TuriSc/Diapasonix/audio/audio_i2s.c

/*
 * Copyright (c) 2020 Raspberry Pi (Trading) Ltd.
 *
 * SPDX-License-Identifier: BSD-3-Clause
 *
 * Adapted from pico-extras/src/rp2_common/pico_audio_i2s/audio_i2s.c
 * Converted from C++ to C for this project.
 */

#include <stdio.h>
#include "audio_i2s.h"
#include "audio_i2s.pio.h"
#include "hardware/pio.h"
#include "hardware/gpio.h"
#include "hardware/dma.h"
#include "hardware/irq.h"
#include "hardware/clocks.h"
#include <assert.h>

#if PICO_AUDIO_I2S_MONO_OUTPUT
#define i2s_dma_configure_size DMA_SIZE_16
#else
#define i2s_dma_configure_size DMA_SIZE_32
#endif

#define audio_pio __CONCAT(pio, PICO_AUDIO_I2S_PIO)
#define GPIO_FUNC_PIOx __CONCAT(GPIO_FUNC_PIO, PICO_AUDIO_I2S_PIO)
#define DREQ_PIOx_TX0 __CONCAT(__CONCAT(DREQ_PIO, PICO_AUDIO_I2S_PIO), _TX0)

struct {
    audio_buffer_t *playing_buffer;
    uint32_t freq;
    uint8_t pio_sm;
    uint8_t dma_channel;
} shared_state;

audio_format_t pio_i2s_consumer_format;
audio_buffer_format_t pio_i2s_consumer_buffer_format = {
    .format = &pio_i2s_consumer_format,
};

static void __isr __time_critical_func(audio_i2s_dma_irq_handler)();

const audio_format_t *audio_i2s_setup(const audio_format_t *intended_audio_format,
                                     const audio_i2s_config_t *config) {
    uint func = GPIO_FUNC_PIOx;
    gpio_set_function(config->data_pin, func);
    gpio_set_function(config->clock_pin_base, func);
    gpio_set_function(config->clock_pin_base + 1, func);

#if PICO_PIO_USE_GPIO_BASE
    if(config->data_pin >= 32 || config->clock_pin_base + 1 >= 32) {
        assert(config->data_pin >= 16 && config->clock_pin_base >= 16);
        pio_set_gpio_base(audio_pio, 16);
    }
#endif
    uint8_t sm = shared_state.pio_sm = config->pio_sm;
    pio_sm_claim(audio_pio, sm);

    const struct pio_program *program =
#if PICO_AUDIO_I2S_CLOCK_PINS_SWAPPED
        &audio_i2s_swapped_program
#else
        &audio_i2s_program
#endif
        ;
    uint offset = pio_add_program(audio_pio, program);

    audio_i2s_program_init(audio_pio, sm, offset, config->data_pin, config->clock_pin_base);

    __mem_fence_release();
    uint8_t dma_channel = config->dma_channel;
    dma_channel_claim(dma_channel);

    shared_state.dma_channel = dma_channel;

    dma_channel_config dma_config = dma_channel_get_default_config(dma_channel);

    channel_config_set_dreq(&dma_config, DREQ_PIOx_TX0 + sm);
    channel_config_set_transfer_data_size(&dma_config, i2s_dma_configure_size);
    dma_channel_configure(dma_channel,
                          &dma_config,
                          &audio_pio->txf[sm],
                          NULL,
                          0,
                          false
    );

    irq_add_shared_handler(DMA_IRQ_0 + PICO_AUDIO_I2S_DMA_IRQ, audio_i2s_dma_irq_handler, PICO_SHARED_IRQ_HANDLER_DEFAULT_ORDER_PRIORITY);
    dma_irqn_set_channel_enabled(PICO_AUDIO_I2S_DMA_IRQ, dma_channel, 1);
    return intended_audio_format;
}

static audio_buffer_pool_t *audio_i2s_consumer;

static void update_pio_frequency(uint32_t sample_freq) {
    uint32_t system_clock_frequency = clock_get_hz(clk_sys);
    assert(system_clock_frequency < 0x40000000);
    uint32_t divider = system_clock_frequency * 4 / sample_freq;
    assert(divider < 0x1000000);
    pio_sm_set_clkdiv_int_frac(audio_pio, shared_state.pio_sm, divider >> 8u, divider & 0xffu);
    shared_state.freq = sample_freq;
}

static audio_buffer_t *wrap_consumer_take(audio_connection_t *connection, bool block) {
    if (connection->producer_pool->format->sample_freq != shared_state.freq) {
        update_pio_frequency(connection->producer_pool->format->sample_freq);
    }
#if PICO_AUDIO_I2S_MONO_INPUT
#if PICO_AUDIO_I2S_MONO_OUTPUT
    return mono_to_mono_consumer_take(connection, block);
#else
    return mono_to_stereo_consumer_take(connection, block);
#endif
#else
#if PICO_AUDIO_I2S_MONO_OUTPUT
    assert(false);
#else
    return stereo_to_stereo_consumer_take(connection, block);
#endif
#endif
}

static void wrap_producer_give(audio_connection_t *connection, audio_buffer_t *buffer) {
    if (connection->producer_pool->format->sample_freq != shared_state.freq) {
        update_pio_frequency(connection->producer_pool->format->sample_freq);
    }
#if PICO_AUDIO_I2S_MONO_INPUT
#if PICO_AUDIO_I2S_MONO_OUTPUT
    assert(false);
#else
    assert(false);
#endif
#else
#if PICO_AUDIO_I2S_MONO_OUTPUT
    assert(false);
#else
    stereo_to_stereo_producer_give(connection, buffer);
#endif
#endif
}

static struct buffer_copying_on_consumer_take_connection m2s_audio_i2s_ct_connection = {
    .core = {
        .consumer_pool_take = wrap_consumer_take,
        .consumer_pool_give = consumer_pool_give_buffer_default,
        .producer_pool_take = producer_pool_take_buffer_default,
        .producer_pool_give = producer_pool_give_buffer_default,
    }
};

static struct producer_pool_blocking_give_connection m2s_audio_i2s_pg_connection = {
    .core = {
        .consumer_pool_take = consumer_pool_take_buffer_default,
        .consumer_pool_give = consumer_pool_give_buffer_default,
        .producer_pool_take = producer_pool_take_buffer_default,
        .producer_pool_give = wrap_producer_give,
    }
};

static void pass_thru_producer_give(audio_connection_t *connection, audio_buffer_t *buffer) {
    queue_full_audio_buffer(connection->consumer_pool, buffer);
}

static void pass_thru_consumer_give(audio_connection_t *connection, audio_buffer_t *buffer) {
    queue_free_audio_buffer(connection->producer_pool, buffer);
}

static struct producer_pool_blocking_give_connection audio_i2s_pass_thru_connection = {
    .core = {
        .consumer_pool_take = consumer_pool_take_buffer_default,
        .consumer_pool_give = pass_thru_consumer_give,
        .producer_pool_take = producer_pool_take_buffer_default,
        .producer_pool_give = pass_thru_producer_give,
    }
};

bool audio_i2s_connect_thru(audio_buffer_pool_t *producer, audio_connection_t *connection) {
    return audio_i2s_connect_extra(producer, false, 2, 256, connection);
}

bool audio_i2s_connect(audio_buffer_pool_t *producer) {
    return audio_i2s_connect_thru(producer, NULL);
}

bool audio_i2s_connect_extra(audio_buffer_pool_t *producer, bool buffer_on_give, uint buffer_count,
                             uint samples_per_buffer, audio_connection_t *connection) {
    printf("Connecting PIO I2S audio\n");

    assert(producer->format->format == AUDIO_BUFFER_FORMAT_PCM_S16);
    pio_i2s_consumer_format.format = AUDIO_BUFFER_FORMAT_PCM_S16;
    pio_i2s_consumer_format.sample_freq = producer->format->sample_freq;
#if PICO_AUDIO_I2S_MONO_OUTPUT
    pio_i2s_consumer_format.channel_count = 1;
    pio_i2s_consumer_buffer_format.sample_stride = 2;
#else
    pio_i2s_consumer_format.channel_count = 2;
    pio_i2s_consumer_buffer_format.sample_stride = 4;
#endif

    audio_i2s_consumer = audio_new_consumer_pool(&pio_i2s_consumer_buffer_format, buffer_count, samples_per_buffer);

    update_pio_frequency(producer->format->sample_freq);

    __mem_fence_release();

    if (!connection) {
        if (producer->format->channel_count == 2) {
#if PICO_AUDIO_I2S_MONO_INPUT
            panic("need to merge channels down\n");
#else
#if PICO_AUDIO_I2S_MONO_OUTPUT
            panic("trying to play stereo thru mono not yet supported");
#else
            printf("Copying stereo to stereo at %d Hz\n", (int) producer->format->sample_freq);
#endif
#endif
        } else {
#if PICO_AUDIO_I2S_MONO_OUTPUT
            printf("Copying mono to mono at %d Hz\n", (int) producer->format->sample_freq);
#else
            printf("Converting mono to stereo at %d Hz\n", (int) producer->format->sample_freq);
#endif
        }
        if (!buffer_count)
            connection = &audio_i2s_pass_thru_connection.core;
        else
            connection = buffer_on_give ? &m2s_audio_i2s_pg_connection.core : &m2s_audio_i2s_ct_connection.core;
    }
    audio_complete_connection(connection, producer, audio_i2s_consumer);
    return true;
}

static inline void audio_start_dma_transfer() {
    assert(!shared_state.playing_buffer);
    audio_buffer_t *ab = take_audio_buffer(audio_i2s_consumer, false);

    shared_state.playing_buffer = ab;
    if (!ab) {
        static uint32_t zero;
        dma_channel_config c = dma_get_channel_config(shared_state.dma_channel);
        channel_config_set_read_increment(&c, false);
        dma_channel_set_config(shared_state.dma_channel, &c, false);
        dma_channel_transfer_from_buffer_now(shared_state.dma_channel, &zero, PICO_AUDIO_I2S_SILENCE_BUFFER_SAMPLE_LENGTH);
        return;
    }
    assert(ab->sample_count);
    assert(ab->format->format->format == AUDIO_BUFFER_FORMAT_PCM_S16);
#if PICO_AUDIO_I2S_MONO_OUTPUT
    assert(ab->format->format->channel_count == 1);
    assert(ab->format->sample_stride == 2);
#else
    assert(ab->format->format->channel_count == 2);
    assert(ab->format->sample_stride == 4);
#endif
    dma_channel_config c = dma_get_channel_config(shared_state.dma_channel);
    channel_config_set_read_increment(&c, true);
    dma_channel_set_config(shared_state.dma_channel, &c, false);
    dma_channel_transfer_from_buffer_now(shared_state.dma_channel, ab->buffer->bytes, ab->sample_count);
}

void __isr __time_critical_func(audio_i2s_dma_irq_handler)() {
#if PICO_AUDIO_I2S_NOOP
    assert(false);
#else
    uint dma_channel = shared_state.dma_channel;
    if (dma_irqn_get_channel_status(PICO_AUDIO_I2S_DMA_IRQ, dma_channel)) {
        dma_irqn_acknowledge_channel(PICO_AUDIO_I2S_DMA_IRQ, dma_channel);
        if (shared_state.playing_buffer) {
            give_audio_buffer(audio_i2s_consumer, shared_state.playing_buffer);
#ifndef NDEBUG
            shared_state.playing_buffer = NULL;
#endif
        }
        audio_start_dma_transfer();
    }
#endif
}

static bool audio_enabled;

void audio_i2s_set_enabled(bool enabled) {
    if (enabled != audio_enabled) {
#ifndef NDEBUG
        if (enabled) {
            puts("Enabling PIO I2S audio\n");
            printf("(on core %d\n", get_core_num());
        }
#endif
        irq_set_enabled(DMA_IRQ_0 + PICO_AUDIO_I2S_DMA_IRQ, enabled);

        if (enabled) {
            audio_start_dma_transfer();
        } else {
            if (shared_state.playing_buffer) {
                give_audio_buffer(audio_i2s_consumer, shared_state.playing_buffer);
                shared_state.playing_buffer = NULL;
            }
        }

        pio_sm_set_enabled(audio_pio, shared_state.pio_sm, enabled);

        audio_enabled = enabled;
    }
}

bool audio_i2s_connect_s8(audio_buffer_pool_t *producer) {
    assert(false);
    return false;
}
