TuriSc/Diapasonix/directional_switch.h

#ifndef DIRECTIONAL_SWITCH_H_
#define DIRECTIONAL_SWITCH_H_
#include "pico/stdlib.h"

#ifdef __cplusplus
extern "C" {
#endif

void directional_switch_init();
void directional_switch_task();

#ifdef __cplusplus
}
#endif

#endif
